Gasman2014/ThermoLogger8/Ver_3V3/Gerbers.png_Combined_Bottom.png

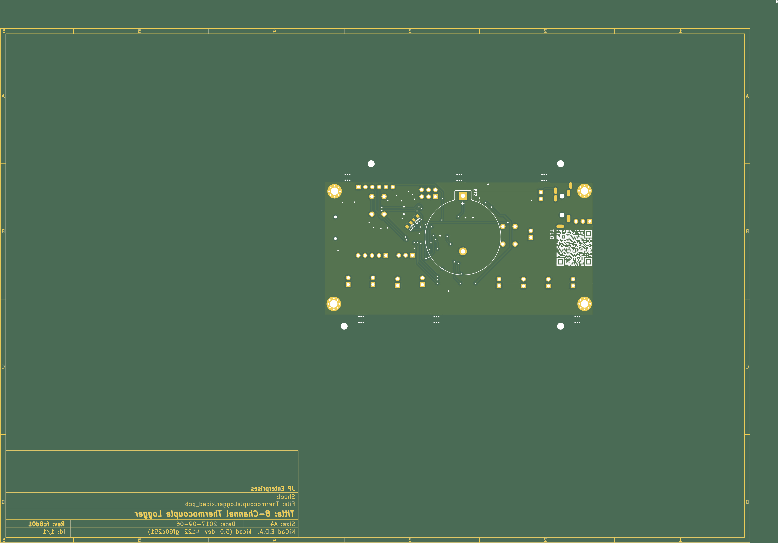
Ver_3V3/Gerbers.png_Combined_Bottom.png
