Gasman2014/ThermoLogger8/Ver_3V3/Plots/620aab/ThermocoupleLogger-B_Cu.png

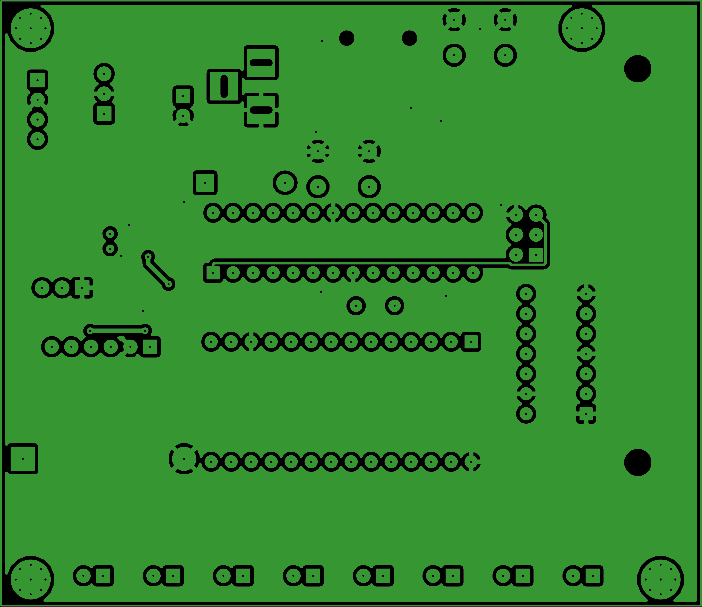
Ver_3V3/Plots/620aab/ThermocoupleLogger-B_Cu.png
