Gasman2014/ThermoLogger8/Ver_3V3/Plots/620aab/ThermocoupleLogger-Cmts_User.png

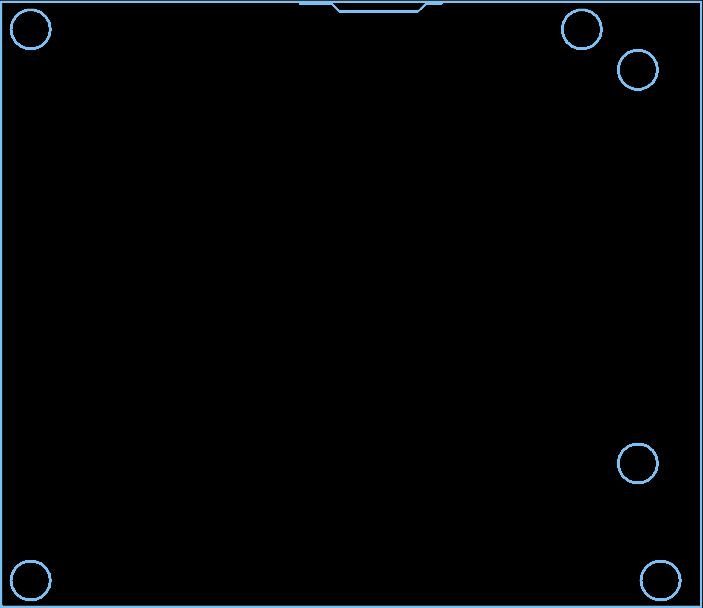
Ver_3V3/Plots/620aab/ThermocoupleLogger-Cmts_User.png
