Gasman2014/ThermoLogger8/Ver_3V3/Plots/620aab/ThermocoupleLogger-F_Fab.png

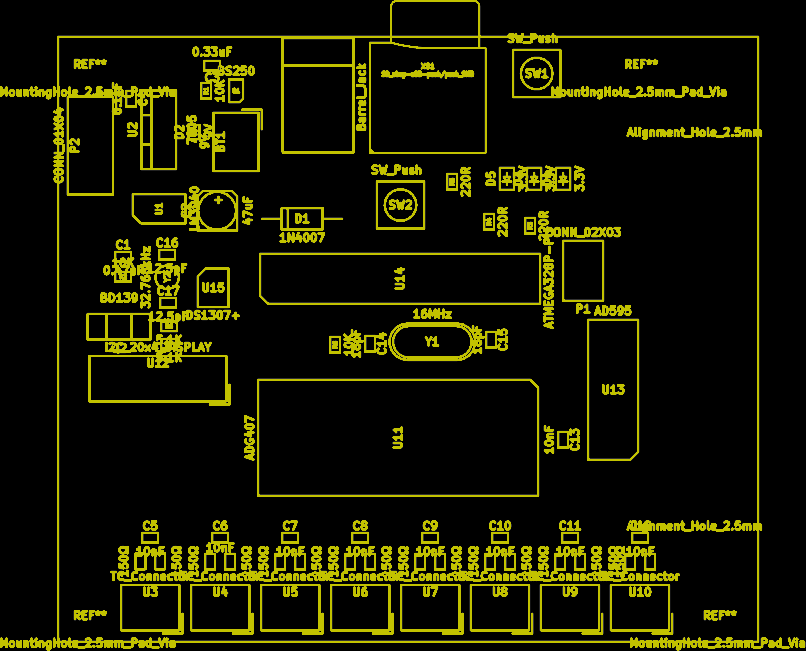
Ver_3V3/Plots/620aab/ThermocoupleLogger-F_Fab.png
