Gasman2014/ThermoLogger8/Ver_3V3/Plots/adfd4f/ThermocoupleLogger-B_CrtYd.png

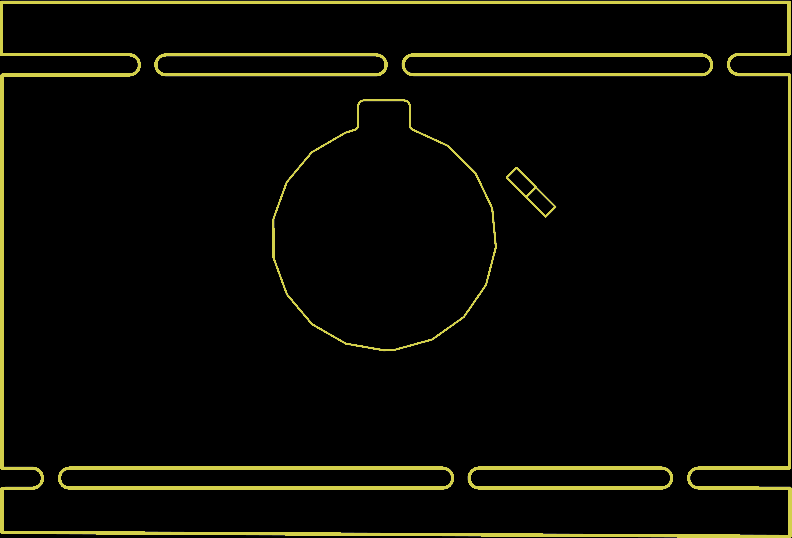
Ver_3V3/Plots/adfd4f/ThermocoupleLogger-B_CrtYd.png
