Gasman2014/ThermoLogger8/Ver_3V3/Plots/adfd4f/ThermocoupleLogger-Cmts_User.png

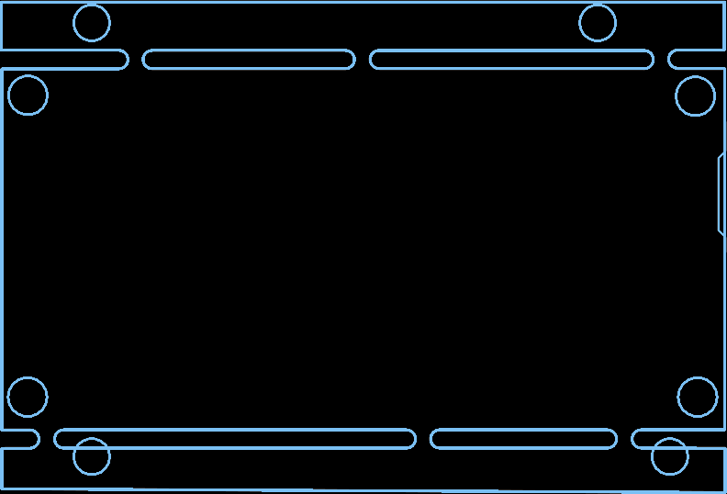
Ver_3V3/Plots/adfd4f/ThermocoupleLogger-Cmts_User.png
