Gasman2014/ThermoLogger8/Ver_3V3/Plots/adfd4f/ThermocoupleLogger-Eco2_User.png

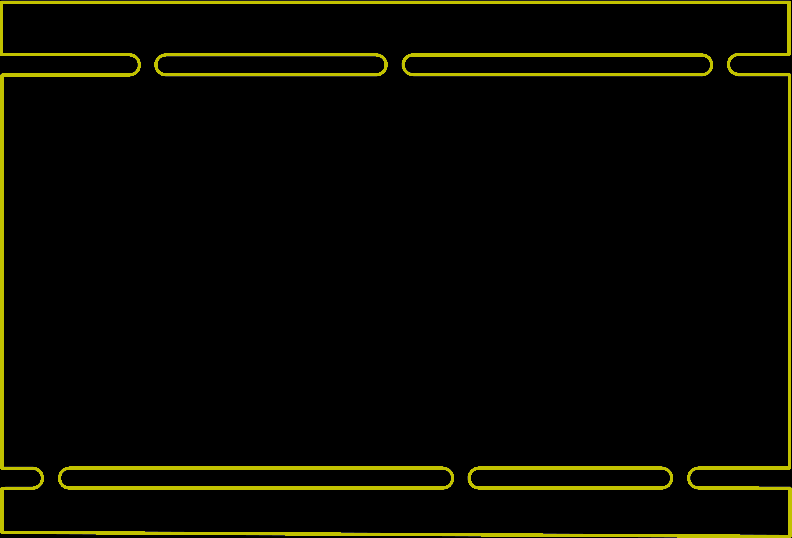
Ver_3V3/Plots/adfd4f/ThermocoupleLogger-Eco2_User.png
