Gasman2014/ThermoLogger8/Ver_3V3/Plots/adfd4f/ThermocoupleLogger-F_CrtYd.png

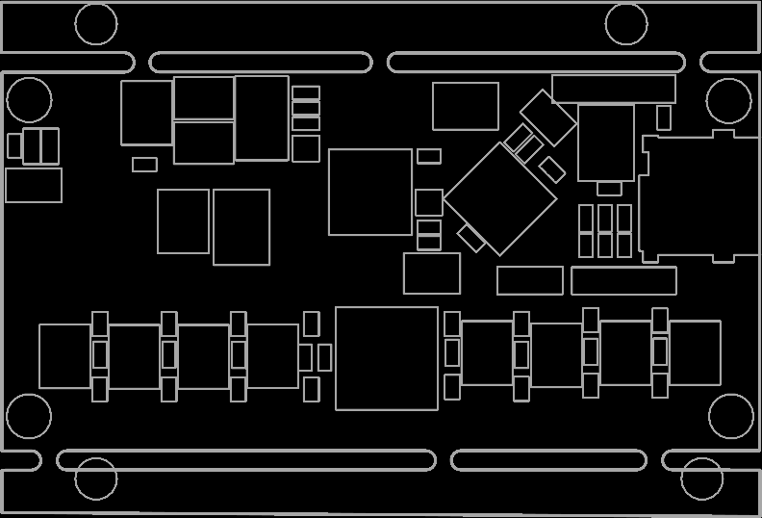
Ver_3V3/Plots/adfd4f/ThermocoupleLogger-F_CrtYd.png
