Gasman2014/ThermoLogger8/Ver_3V3/Plots/adfd4f/ThermocoupleLogger-In2_Cu.png

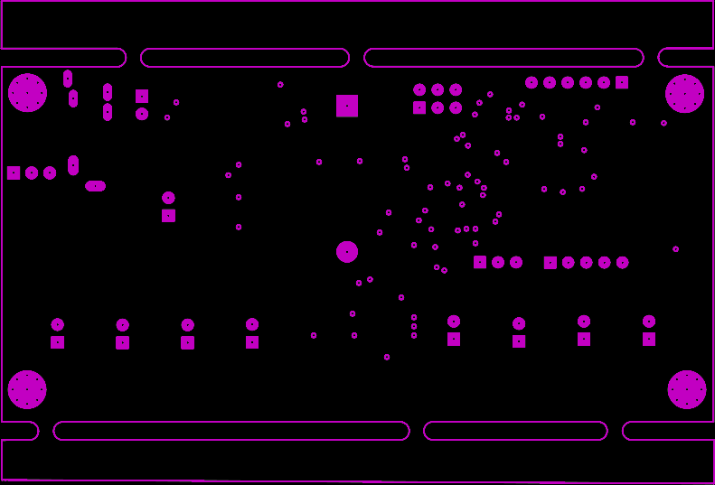
Ver_3V3/Plots/adfd4f/ThermocoupleLogger-In2_Cu.png
