Gasman2014/ThermoLogger8/Ver_3V3/Plots/web/thumbs/th_ThermocoupleLogger-B_Adhes.png

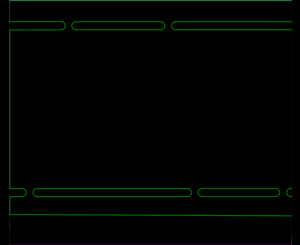
Ver_3V3/Plots/web/thumbs/th_ThermocoupleLogger-B_Adhes.png
