Gasman2014/ThermoLogger8/Ver_3V3/Plots/web/thumbs/th_ThermocoupleLogger-F_CrtYd.png

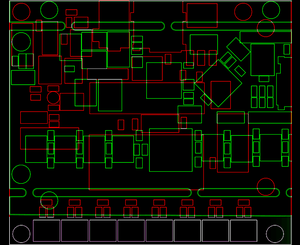
Ver_3V3/Plots/web/thumbs/th_ThermocoupleLogger-F_CrtYd.png
