Gasman2014/ThermoLogger8/Ver_5V/Plots/3c9fec/ThermocoupleLogger-B_Cu.png

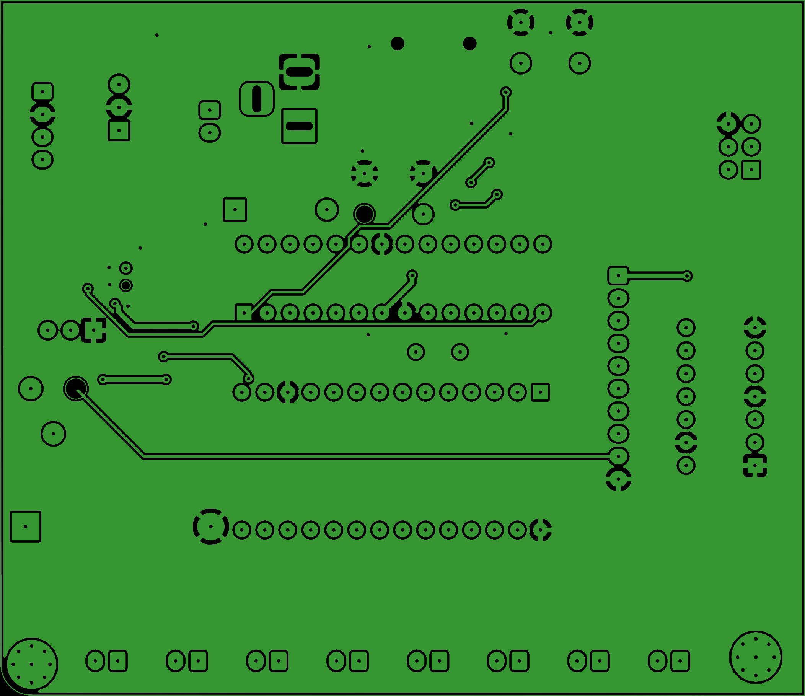
Ver_5V/Plots/3c9fec/ThermocoupleLogger-B_Cu.png
