Gasman2014/ThermoLogger8/Ver_5V/Plots/b2096b/ThermocoupleLogger-B_Mask.png

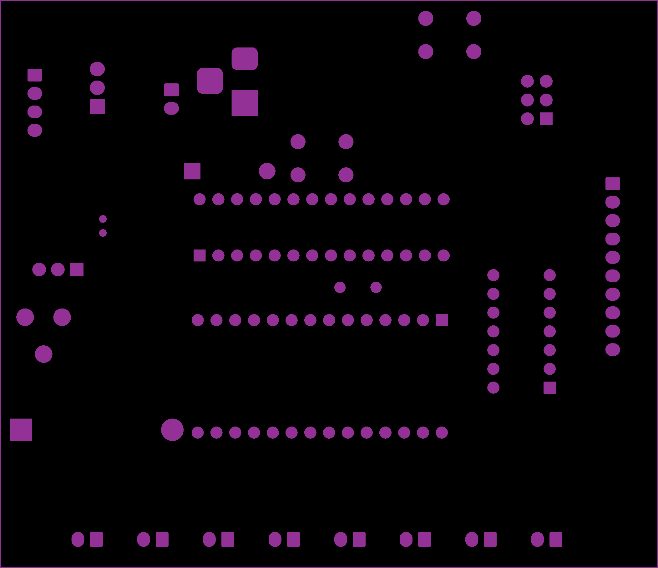
Ver_5V/Plots/b2096b/ThermocoupleLogger-B_Mask.png
