Gasman2014/ThermoLogger8/Ver_5V/Plots/b2096b/ThermocoupleLogger-F_Paste.png

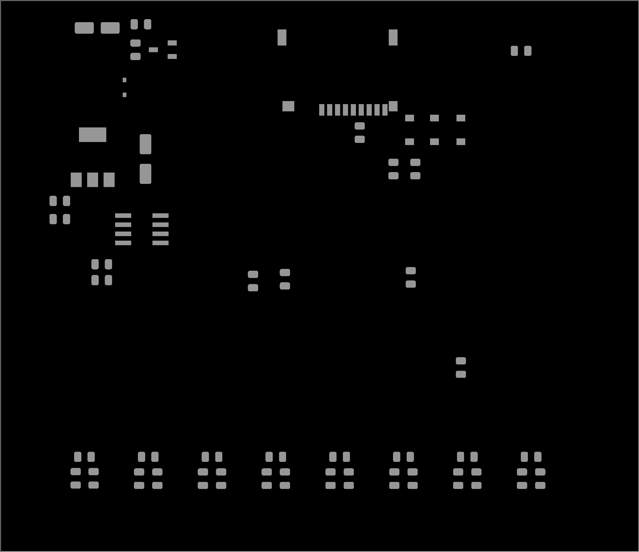
Ver_5V/Plots/b2096b/ThermocoupleLogger-F_Paste.png
