Gasman2014/ThermoLogger8/Ver_5V/Plots/b2096b/ThermocoupleLogger-In2_Cu.png

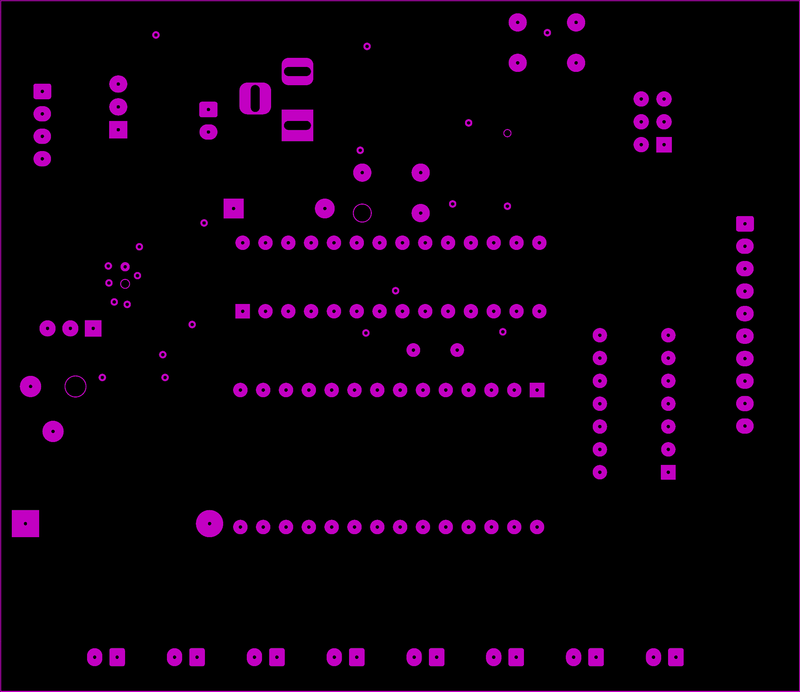
Ver_5V/Plots/b2096b/ThermocoupleLogger-In2_Cu.png
