Gasman2014/ThermoLogger8/Ver_5V/Plots/diff-3c9fec-b2096b/ThermocoupleLogger-F_CrtYd.png

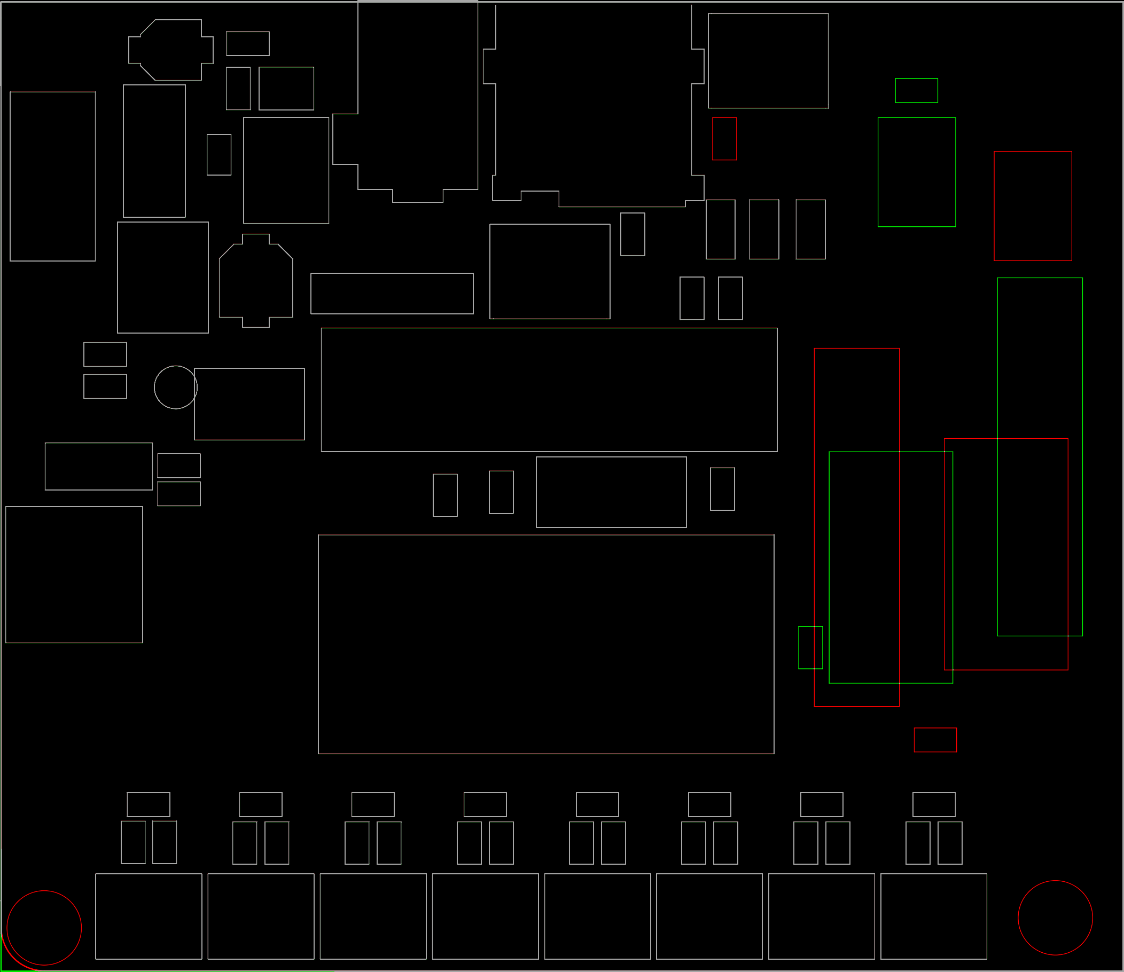
Ver_5V/Plots/diff-3c9fec-b2096b/ThermocoupleLogger-F_CrtYd.png
