Gasman2014/ThermoLogger8/Ver_5V/Plots/web/thumbs/th_ThermocoupleLogger-B_Cu.png

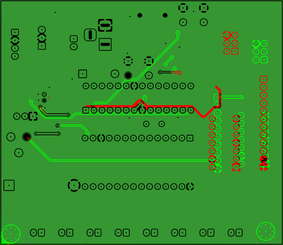
Ver_5V/Plots/web/thumbs/th_ThermocoupleLogger-B_Cu.png
