Gasman2014/ThermoLogger8/Ver_5V/Plots/web/thumbs/th_ThermocoupleLogger-F_Fab.png

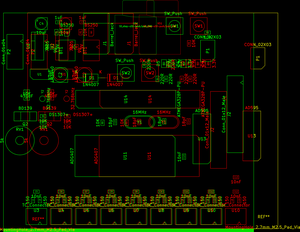
Ver_5V/Plots/web/thumbs/th_ThermocoupleLogger-F_Fab.png
