Gasman2014/ThermoLogger8/Ver_5V/Plots/diff-3c9fec-b2096b/diff.txt

5,6c5,6
<     (drawings 12)
<     (tracks 555)
---
>     (drawings 13)
>     (tracks 669)
8c8
<     (modules 73)
---
>     (modules 75)
46c46
<     (zone_clearance 0.25)
---
>     (zone_clearance 0.1)
65c65
<     (pad_size 1.1 1.3)
---
>     (pad_size 1.2 1.4)
274c274
<     (clearance 0.25)
---
>     (clearance 0.2)
287c287
<     (at 176.8 97.2 270)
---
>     (at 162.3 102.8 270)
475a476,480
>     (model ${KICUST3DMOD}/Connectors.3dshapes/BarrelJack.STEP
>       (offset (xyz -6 0 0))
>       (scale (xyz 1 1 1))
>       (rotate (xyz -90 0 -90))
>     )
1191c1196
<   (module JP_Connectors:Conn_uSDcard (layer F.Cu) (tedit 5718CF45) (tstamp 59932149)
---
>   (module JP_Connectors:Conn_uSDcard (layer F.Cu) (tedit 5C3CAC0E) (tstamp 59932149)
1340c1345
<     (at 168.275 124.841 180)
---
>     (at 177.4 123.8 180)
1559c1564
<     (at 167.8 88.4 180)
---
>     (at 177 91.1 180)
3357c3362
<     (at 158.115 123.571 270)
---
>     (at 168 130.9)
3362c3367
<     (fp_text reference C13 (at 0 -1.65 270) (layer F.SilkS)
---
>     (fp_text reference C13 (at 0 -1.65) (layer F.SilkS)
3365c3370
<     (fp_text value 10nF (at 0 1.65 270) (layer F.Fab)
---
>     (fp_text value 10nF (at 0 1.65) (layer F.Fab)
3368c3373
<     (fp_text user %R (at 0 0 270) (layer F.Fab)
---
>     (fp_text user %R (at 0 0) (layer F.Fab)
3381c3386
<     (pad 2 smd roundrect (at 0.9375 0 270) (size 0.975 1.4) (layers F.Cu F.Paste F.Mask) (roundrect_rratio 0.25)
---
>     (pad 2 smd roundrect (at 0.9375 0) (size 0.975 1.4) (layers F.Cu F.Paste F.Mask) (roundrect_rratio 0.25)
3383c3388
<     (pad 1 smd roundrect (at -0.9375 0 270) (size 0.975 1.4) (layers F.Cu F.Paste F.Mask) (roundrect_rratio 0.25)
---
>     (pad 1 smd roundrect (at -0.9375 0) (size 0.975 1.4) (layers F.Cu F.Paste F.Mask) (roundrect_rratio 0.25)
3587c3592
<     (at 166.5 79.4)
---
>     (at 151.3 83.2375 90)
3592c3597
<     (fp_text reference R9 (at 0 -1.65) (layer F.SilkS)
---
>     (fp_text reference R9 (at 0 -1.65 90) (layer F.SilkS)
3595c3600
<     (fp_text value 10K (at 0 1.65) (layer F.Fab)
---
>     (fp_text value 10K (at 0 1.65 90) (layer F.Fab)
3598c3603
<     (fp_text user %R (at 0 0) (layer F.Fab)
---
>     (fp_text user %R (at 0 0 90) (layer F.Fab)
3611c3616
<     (pad 2 smd roundrect (at 0.9375 0) (size 0.975 1.4) (layers F.Cu F.Paste F.Mask) (roundrect_rratio 0.25)
---
>     (pad 2 smd roundrect (at 0.9375 0 90) (size 0.975 1.4) (layers F.Cu F.Paste F.Mask) (roundrect_rratio 0.25)
3613c3618
<     (pad 1 smd roundrect (at -0.9375 0) (size 0.975 1.4) (layers F.Cu F.Paste F.Mask) (roundrect_rratio 0.25)
---
>     (pad 1 smd roundrect (at -0.9375 0 90) (size 0.975 1.4) (layers F.Cu F.Paste F.Mask) (roundrect_rratio 0.25)
3621a3627,3681
>   (module MountingHole:MountingHole_2.7mm_M2.5_Pad_Via (layer F.Cu) (tedit 56DDBBFF) (tstamp 5C3CC69D)
>     (at 97.4 145.8)
>     (descr "Mounting Hole 2.7mm")
>     (tags "mounting hole 2.7mm")
>     (attr virtual)
>     (fp_text reference REF** (at 0 -3.7) (layer F.SilkS)
>       (effects (font (size 1 1) (thickness 0.15)))
>     )
>     (fp_text value MountingHole_2.7mm_M2.5_Pad_Via (at 0 3.7) (layer F.Fab)
>       (effects (font (size 1 1) (thickness 0.15)))
>     )
>     (fp_circle (center 0 0) (end 2.95 0) (layer F.CrtYd) (width 0.05))
>     (fp_circle (center 0 0) (end 2.7 0) (layer Cmts.User) (width 0.15))
>     (fp_text user %R (at 0.3 0) (layer F.Fab)
>       (effects (font (size 1 1) (thickness 0.15)))
>     )
>     (pad 1 thru_hole circle (at 1.431891 -1.431891) (size 0.8 0.8) (drill 0.5) (layers *.Cu *.Mask))
>     (pad 1 thru_hole circle (at 0 -2.025) (size 0.8 0.8) (drill 0.5) (layers *.Cu *.Mask))
>     (pad 1 thru_hole circle (at -1.431891 -1.431891) (size 0.8 0.8) (drill 0.5) (layers *.Cu *.Mask))
>     (pad 1 thru_hole circle (at -2.025 0) (size 0.8 0.8) (drill 0.5) (layers *.Cu *.Mask))
>     (pad 1 thru_hole circle (at -1.431891 1.431891) (size 0.8 0.8) (drill 0.5) (layers *.Cu *.Mask))
>     (pad 1 thru_hole circle (at 0 2.025) (size 0.8 0.8) (drill 0.5) (layers *.Cu *.Mask))
>     (pad 1 thru_hole circle (at 1.431891 1.431891) (size 0.8 0.8) (drill 0.5) (layers *.Cu *.Mask))
>     (pad 1 thru_hole circle (at 2.025 0) (size 0.8 0.8) (drill 0.5) (layers *.Cu *.Mask))
>     (pad 1 thru_hole circle (at 0 0) (size 5.4 5.4) (drill 2.7) (layers *.Cu *.Mask))
>   )
> 
>   (module MountingHole:MountingHole_2.7mm_M2.5_Pad_Via (layer F.Cu) (tedit 56DDBBFF) (tstamp 5C3CC6BC)
>     (at 177.5 145)
>     (descr "Mounting Hole 2.7mm")
>     (tags "mounting hole 2.7mm")
>     (attr virtual)
>     (fp_text reference REF** (at 0 -3.7) (layer F.SilkS)
>       (effects (font (size 1 1) (thickness 0.15)))
>     )
>     (fp_text value MountingHole_2.7mm_M2.5_Pad_Via (at 0 3.7) (layer F.Fab)
>       (effects (font (size 1 1) (thickness 0.15)))
>     )
>     (fp_circle (center 0 0) (end 2.95 0) (layer F.CrtYd) (width 0.05))
>     (fp_circle (center 0 0) (end 2.7 0) (layer Cmts.User) (width 0.15))
>     (fp_text user %R (at 0.3 0) (layer F.Fab)
>       (effects (font (size 1 1) (thickness 0.15)))
>     )
>     (pad 1 thru_hole circle (at 1.431891 -1.431891) (size 0.8 0.8) (drill 0.5) (layers *.Cu *.Mask))
>     (pad 1 thru_hole circle (at 0 -2.025) (size 0.8 0.8) (drill 0.5) (layers *.Cu *.Mask))
>     (pad 1 thru_hole circle (at -1.431891 -1.431891) (size 0.8 0.8) (drill 0.5) (layers *.Cu *.Mask))
>     (pad 1 thru_hole circle (at -2.025 0) (size 0.8 0.8) (drill 0.5) (layers *.Cu *.Mask))
>     (pad 1 thru_hole circle (at -1.431891 1.431891) (size 0.8 0.8) (drill 0.5) (layers *.Cu *.Mask))
>     (pad 1 thru_hole circle (at 0 2.025) (size 0.8 0.8) (drill 0.5) (layers *.Cu *.Mask))
>     (pad 1 thru_hole circle (at 1.431891 1.431891) (size 0.8 0.8) (drill 0.5) (layers *.Cu *.Mask))
>     (pad 1 thru_hole circle (at 2.025 0) (size 0.8 0.8) (drill 0.5) (layers *.Cu *.Mask))
>     (pad 1 thru_hole circle (at 0 0) (size 5.4 5.4) (drill 2.7) (layers *.Cu *.Mask))
>   )
> 
>   (gr_arc (start 97.4 145.8) (end 94 145.8) (angle -90) (layer Edge.Cuts) (width 0.1))
3625c3685
<   (gr_text "©2017, JP Enterprises" (at 95.758 102.616 270) (layer F.SilkS)
---
>   (gr_text "©2019, JP Enterprises" (at 95.758 102.616 270) (layer F.SilkS)
3640,3641c3700,3701
<   (gr_line (start 93.98 149.225) (end 182.88 149.225) (layer Edge.Cuts) (width 0.1))
<   (gr_line (start 93.98 72.39) (end 93.98 149.225) (layer Edge.Cuts) (width 0.1))
---
>   (gr_line (start 97.4 149.2) (end 182.88 149.225) (layer Edge.Cuts) (width 0.1))
>   (gr_line (start 93.98 72.39) (end 94 145.8) (layer Edge.Cuts) (width 0.1))
3667,3668d3726
<   (segment (start 158.115 122.571) (end 160.385 122.571) (width 0.5) (layer F.Cu) (net 1) (status 30))
<   (segment (start 160.385 122.571) (end 160.655 122.301) (width 0.5) (layer F.Cu) (net 1) (status 30))
3706d3763
<   (via (at 109.1946 102.9716) (size 0.8) (drill 0.4) (layers F.Cu B.Cu) (net 1))
3726a3784,3788
>   (segment (start 167.0625 129.9375) (end 167.0625 130.9) (width 0.5) (layer F.Cu) (net 1) (status 20))
>   (segment (start 162.425 125.3) (end 167.0625 129.9375) (width 0.5) (layer F.Cu) (net 1) (status 10))
>   (segment (start 162.3 125.3) (end 162.425 125.3) (width 0.5) (layer F.Cu) (net 1) (status 30))
>   (segment (start 112.6005 78.135) (end 112.776 78.3105) (width 0.5) (layer F.Cu) (net 1))
>   (segment (start 112.6005 75.692) (end 112.6005 78.135) (width 0.5) (layer F.Cu) (net 1))
3731d3792
<   (segment (start 115.279426 108.407535) (end 108.449333 108.407535) (width 0.5) (layer B.Cu) (net 2))
3734,3735d3794
<   (segment (start 106.611743 106.569945) (end 106.611743 105.899326) (width 0.5) (layer B.Cu) (net 2))
<   (segment (start 108.449333 108.407535) (end 106.611743 106.569945) (width 0.5) (layer B.Cu) (net 2))
3742a3802,3805
>   (segment (start 115.279426 108.407535) (end 108.611433 108.407535) (width 0.5) (layer B.Cu) (net 2))
>   (segment (start 108.611433 108.407535) (end 107.011742 106.807844) (width 0.5) (layer B.Cu) (net 2))
>   (segment (start 107.011742 106.807844) (end 107.011742 106.299325) (width 0.5) (layer B.Cu) (net 2))
>   (segment (start 107.011742 106.299325) (end 106.611743 105.899326) (width 0.5) (layer B.Cu) (net 2))
3767,3773d3829
<   (segment (start 141.224 100.44537) (end 140.716 100.95337) (width 0.5) (layer F.Cu) (net 3))
<   (segment (start 141.224 99.314) (end 141.224 100.44537) (width 0.5) (layer F.Cu) (net 3) (status 10))
<   (segment (start 140.716 100.95337) (end 140.716 101.854) (width 0.5) (layer F.Cu) (net 3))
<   (via (at 137.922 104.648) (size 0.8) (drill 0.4) (layers F.Cu B.Cu) (net 3))
<   (segment (start 140.716 101.854) (end 137.922 104.648) (width 0.5) (layer F.Cu) (net 3))
<   (segment (start 137.922 104.648) (end 137.922 105.156) (width 0.5) (layer B.Cu) (net 3))
<   (segment (start 137.922 105.156) (end 136.144 106.934) (width 0.5) (layer B.Cu) (net 3) (status 20))
3785,3788c3841,3865
<   (segment (start 102.23754 101.27004) (end 101.2975 100.33) (width 0.5) (layer F.Cu) (net 3) (status 20))
<   (segment (start 102.23754 104.335556) (end 102.23754 101.27004) (width 0.5) (layer F.Cu) (net 3))
<   (segment (start 102.318556 104.335556) (end 107.1395 109.1565) (width 0.5) (layer F.Cu) (net 3) (status 20))
<   (segment (start 102.23754 104.335556) (end 102.318556 104.335556) (width 0.5) (layer F.Cu) (net 3))
---
>   (segment (start 139.481795 103.596205) (end 139.481795 102.774979) (width 0.5) (layer B.Cu) (net 3))
>   (via (at 139.481795 102.774979) (size 0.8) (drill 0.4) (layers F.Cu B.Cu) (net 3))
>   (segment (start 141.224 101.032774) (end 139.481795 102.774979) (width 0.5) (layer F.Cu) (net 3))
>   (segment (start 141.224 99.314) (end 141.224 101.032774) (width 0.5) (layer F.Cu) (net 3) (status 10))
>   (segment (start 136.144 106.934) (end 139.481795 103.596205) (width 0.5) (layer B.Cu) (net 3) (status 10))
>   (segment (start 153.67 119.259338) (end 153.67 115.697) (width 0.5) (layer F.Cu) (net 3) (status 20))
>   (segment (start 166.510672 132.10001) (end 153.67 119.259338) (width 0.5) (layer F.Cu) (net 3))
>   (segment (start 169.489328 132.10001) (end 166.510672 132.10001) (width 0.5) (layer F.Cu) (net 3))
>   (segment (start 171.080001 130.509337) (end 169.489328 132.10001) (width 0.5) (layer F.Cu) (net 3))
>   (segment (start 171.080001 118.095999) (end 171.080001 130.509337) (width 0.5) (layer F.Cu) (net 3))
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
<   (segment (start 140.927 88.68) (end 142.92701 90.68001) (width 0.25) (layer F.Cu) (net 26))
---
>   (segment (start 153.432 92.924) (end 154.282 92.074) (width 0.25) (layer F.Cu) (net 26) (status 20))
>   (segment (start 147.408413 92.924) (end 153.432 92.924) (width 0.25) (layer F.Cu) (net 26))
>   (segment (start 147.3 92.815587) (end 147.408413 92.924) (width 0.25) (layer F.Cu) (net 26))
>   (segment (start 147.3 93.5305) (end 147.3 92.815587) (width 0.25) (layer F.Cu) (net 26))
>   (segment (start 148.717 94.9475) (end 147.3 93.5305) (width 0.25) (layer F.Cu) (net 26) (status 10))
>   (segment (start 142.92701 90.68001) (end 145.253012 90.68001) (width 0.25) (layer F.Cu) (net 26))
3985a4062,4064
>   (segment (start 140.927 88.68) (end 142.92701 90.68001) (width 0.25) (layer F.Cu) (net 26))
>   (segment (start 145.253012 90.68001) (end 147.3 92.726998) (width 0.25) (layer F.Cu) (net 26))
>   (segment (start 147.3 92.726998) (end 147.3 92.815587) (width 0.25) (layer F.Cu) (net 26))
3994,3998c4073,4077
<   (segment (start 150.114 94.996) (end 150.368 95.25) (width 0.25) (layer B.Cu) (net 27))
<   (via (at 150.368 95.25) (size 0.8) (drill 0.4) (layers F.Cu B.Cu) (net 27))
<   (segment (start 144.272 94.996) (end 150.114 94.996) (width 0.25) (layer B.Cu) (net 27))
<   (segment (start 151.4625 95.25) (end 151.765 94.9475) (width 0.25) (layer F.Cu) (net 27) (status 30))
<   (segment (start 150.368 95.25) (end 151.4625 95.25) (width 0.25) (layer F.Cu) (net 27) (status 20))
---
>   (segment (start 151.765 94.9475) (end 150.64353 93.82603) (width 0.25) (layer F.Cu) (net 27) (status 10))
>   (segment (start 144.272 94.996) (end 147.694734 94.996) (width 0.25) (layer B.Cu) (net 27))
>   (segment (start 147.694734 94.996) (end 148.864704 93.82603) (width 0.25) (layer B.Cu) (net 27))
>   (segment (start 150.64353 93.82603) (end 148.864704 93.82603) (width 0.25) (layer F.Cu) (net 27))
>   (via (at 148.864704 93.82603) (size 0.8) (drill 0.4) (layers F.Cu B.Cu) (net 27))
4052,4057d4130
<   (segment (start 158.011 79.303) (end 158.011 80.717213) (width 0.25) (layer F.Cu) (net 45) (status 10))
<   (segment (start 158.011 80.717213) (end 160.147 82.853213) (width 0.25) (layer F.Cu) (net 45))
<   (segment (start 160.147 82.853213) (end 160.147 84.709) (width 0.25) (layer F.Cu) (net 45))
<   (segment (start 155.502787 84.709) (end 160.147 84.709) (width 0.25) (layer F.Cu) (net 45))
<   (segment (start 151.511 79.303) (end 151.511 80.717213) (width 0.25) (layer F.Cu) (net 45) (status 10))
<   (segment (start 151.511 80.717213) (end 155.502787 84.709) (width 0.25) (layer F.Cu) (net 45))
4058a4132,4150
>   (segment (start 151.511 79.303) (end 158.011 79.303) (width 0.25) (layer F.Cu) (net 45) (status 30))
>   (segment (start 170.283 79.303) (end 177 86.02) (width 0.25) (layer F.Cu) (net 45) (status 20))
>   (segment (start 158.011 79.303) (end 170.283 79.303) (width 0.25) (layer F.Cu) (net 45) (status 10))
>   (segment (start 151.511 82.089) (end 151.3 82.3) (width 0.25) (layer F.Cu) (net 45) (status 30))
>   (segment (start 151.511 79.303) (end 151.511 82.089) (width 0.25) (layer F.Cu) (net 45) (status 30))
>   (via (at 149.85 82.52) (size 0.8) (drill 0.4) (layers F.Cu B.Cu) (net 45))
>   (segment (start 151.08 82.52) (end 151.3 82.3) (width 0.25) (layer F.Cu) (net 45) (status 30))
>   (segment (start 149.85 82.52) (end 151.08 82.52) (width 0.25) (layer F.Cu) (net 45) (status 20))
>   (segment (start 120.904 106.934) (end 121.200476 107.230476) (width 0.25) (layer F.Cu) (net 45) (status 30))
>   (segment (start 123.940464 104.644003) (end 121.600475 106.983992) (width 0.25) (layer B.Cu) (net 45) (status 20))
>   (segment (start 127.398999 104.644003) (end 123.940464 104.644003) (width 0.25) (layer B.Cu) (net 45))
>   (segment (start 121.200476 107.230476) (end 121.200476 107.383991) (width 0.25) (layer F.Cu) (net 45) (status 30))
>   (segment (start 121.600475 106.983992) (end 121.200476 107.383991) (width 0.25) (layer B.Cu) (net 45) (status 30))
>   (segment (start 149.85 84.413002) (end 136.926001 97.337001) (width 0.25) (layer B.Cu) (net 45))
>   (segment (start 132.478999 98.571001) (end 132.478999 99.564003) (width 0.25) (layer B.Cu) (net 45))
>   (segment (start 132.478999 99.564003) (end 127.398999 104.644003) (width 0.25) (layer B.Cu) (net 45))
>   (segment (start 136.926001 97.337001) (end 133.712999 97.337001) (width 0.25) (layer B.Cu) (net 45))
>   (segment (start 133.712999 97.337001) (end 132.478999 98.571001) (width 0.25) (layer B.Cu) (net 45))
>   (segment (start 149.85 82.52) (end 149.85 84.413002) (width 0.25) (layer B.Cu) (net 45))
4060a4153,4166
>   (segment (start 152.509001 99.854001) (end 151.924001 100.439001) (width 0.25) (layer F.Cu) (net 46))
>   (segment (start 151.924001 100.439001) (end 149.969001 100.439001) (width 0.25) (layer F.Cu) (net 46))
>   (segment (start 174.46 88.56) (end 175.635001 89.735001) (width 0.25) (layer F.Cu) (net 46))
>   (segment (start 170.408402 104.085013) (end 169.141598 104.085013) (width 0.25) (layer F.Cu) (net 46))
>   (segment (start 177.920003 89.735001) (end 178.175001 89.989999) (width 0.25) (layer F.Cu) (net 46))
>   (segment (start 178.175001 89.989999) (end 178.175001 96.318414) (width 0.25) (layer F.Cu) (net 46))
>   (segment (start 169.141598 104.085013) (end 163.245584 98.188999) (width 0.25) (layer F.Cu) (net 46))
>   (segment (start 175.635001 89.735001) (end 177.920003 89.735001) (width 0.25) (layer F.Cu) (net 46))
>   (segment (start 178.175001 96.318414) (end 170.408402 104.085013) (width 0.25) (layer F.Cu) (net 46))
>   (segment (start 153.383999 98.188999) (end 152.509001 99.063997) (width 0.25) (layer F.Cu) (net 46))
>   (segment (start 152.509001 99.063997) (end 152.509001 99.854001) (width 0.25) (layer F.Cu) (net 46))
>   (segment (start 163.245584 98.188999) (end 153.383999 98.188999) (width 0.25) (layer F.Cu) (net 46))
>   (segment (start 149.969001 100.439001) (end 149.643999 100.113999) (width 0.25) (layer F.Cu) (net 46))
>   (segment (start 149.643999 100.113999) (end 148.844 99.314) (width 0.25) (layer F.Cu) (net 46))
4064a4171,4197
>   (segment (start 159.015001 89.599001) (end 148.427597 89.599001) (width 0.25) (layer F.Cu) (net 47))
>   (segment (start 148 90.026598) (end 148 90.3) (width 0.25) (layer F.Cu) (net 47))
>   (segment (start 161.229003 87.384999) (end 159.015001 89.599001) (width 0.25) (layer F.Cu) (net 47))
>   (segment (start 148.427597 89.599001) (end 148 90.026598) (width 0.25) (layer F.Cu) (net 47))
>   (segment (start 175.824999 87.384999) (end 161.229003 87.384999) (width 0.25) (layer F.Cu) (net 47))
>   (via (at 148 90.3) (size 0.8) (drill 0.4) (layers F.Cu B.Cu) (net 47))
>   (segment (start 177 88.56) (end 175.824999 87.384999) (width 0.25) (layer F.Cu) (net 47) (status 10))
>   (via (at 146 92.5) (size 0.8) (drill 0.4) (layers F.Cu B.Cu) (net 47))
>   (segment (start 146 92.3) (end 146 92.5) (width 0.25) (layer B.Cu) (net 47))
>   (segment (start 148 90.3) (end 146 92.3) (width 0.25) (layer B.Cu) (net 47))
>   (segment (start 144.7755 92.5) (end 144.018 91.7425) (width 0.25) (layer F.Cu) (net 47) (status 20))
>   (segment (start 146 92.5) (end 144.7755 92.5) (width 0.25) (layer F.Cu) (net 47))
>   (segment (start 146.304 97.73115) (end 148.27514 95.76001) (width 0.25) (layer F.Cu) (net 48))
>   (segment (start 146.304 99.314) (end 146.304 97.73115) (width 0.25) (layer F.Cu) (net 48) (status 10))
>   (segment (start 158.975001 91.298999) (end 161.876002 94.2) (width 0.25) (layer F.Cu) (net 48))
>   (segment (start 145.327 88.68) (end 147.945999 91.298999) (width 0.25) (layer F.Cu) (net 48))
>   (segment (start 145.327 87.63) (end 145.327 88.68) (width 0.25) (layer F.Cu) (net 48) (status 10))
>   (segment (start 147.945999 91.298999) (end 158.975001 91.298999) (width 0.25) (layer F.Cu) (net 48))
>   (segment (start 161.876002 94.336012) (end 163.3 95.76001) (width 0.25) (layer F.Cu) (net 48))
>   (segment (start 161.876002 94.2) (end 161.876002 94.336012) (width 0.25) (layer F.Cu) (net 48))
>   (segment (start 148.27514 95.76001) (end 163.3 95.76001) (width 0.25) (layer F.Cu) (net 48))
>   (segment (start 169.307998 103.615002) (end 170.242002 103.615002) (width 0.25) (layer F.Cu) (net 48))
>   (segment (start 163.3 95.76001) (end 163.3 97.607004) (width 0.25) (layer F.Cu) (net 48))
>   (segment (start 163.3 97.607004) (end 169.307998 103.615002) (width 0.25) (layer F.Cu) (net 48))
>   (segment (start 177 96.857004) (end 177 92.2) (width 0.25) (layer F.Cu) (net 48))
>   (segment (start 177 92.2) (end 177 91.1) (width 0.25) (layer F.Cu) (net 48))
>   (segment (start 170.242002 103.615002) (end 177 96.857004) (width 0.25) (layer F.Cu) (net 48))
4122,4135c4255,4264
<   (segment (start 142.638999 95.973997) (end 142.638999 99.854001) (width 0.25) (layer F.Cu) (net 52))
<   (segment (start 142.638999 99.854001) (end 148.093986 105.308988) (width 0.25) (layer F.Cu) (net 52))
<   (segment (start 148.093986 105.308988) (end 152.298988 105.308988) (width 0.25) (layer F.Cu) (net 52))
<   (segment (start 103.1725 102.87) (end 105.456888 100.585612) (width 0.25) (layer F.Cu) (net 52) (status 10))
<   (segment (start 115.680613 97.934999) (end 131.528601 97.934999) (width 0.25) (layer F.Cu) (net 52))
<   (segment (start 131.528601 97.934999) (end 132.890999 96.572601) (width 0.25) (layer F.Cu) (net 52))
<   (segment (start 153.124001 106.134001) (end 153.924 106.934) (width 0.25) (layer F.Cu) (net 52) (status 30))
<   (segment (start 141.352001 94.686999) (end 142.638999 95.973997) (width 0.25) (layer F.Cu) (net 52))
<   (segment (start 133.579999 94.686999) (end 141.352001 94.686999) (width 0.25) (layer F.Cu) (net 52))
<   (segment (start 105.456888 100.585612) (end 113.03 100.585612) (width 0.25) (layer F.Cu) (net 52))
<   (segment (start 113.03 100.585612) (end 115.680613 97.934999) (width 0.25) (layer F.Cu) (net 52))
<   (segment (start 132.890999 96.572601) (end 132.890999 95.375999) (width 0.25) (layer F.Cu) (net 52))
<   (segment (start 132.890999 95.375999) (end 133.579999 94.686999) (width 0.25) (layer F.Cu) (net 52))
<   (segment (start 152.298988 105.308988) (end 153.124001 106.134001) (width 0.25) (layer F.Cu) (net 52) (status 20))
---
>   (segment (start 108.107897 109.3) (end 103.61999 104.812093) (width 0.25) (layer B.Cu) (net 52))
>   (via (at 103.61999 104.246408) (size 0.8) (drill 0.4) (layers F.Cu B.Cu) (net 52))
>   (segment (start 103.61999 104.812093) (end 103.61999 104.246408) (width 0.25) (layer B.Cu) (net 52))
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
>         (xy 140.538394 112.207424) (xy 140.855424 111.890394) (xy 141.027 111.476174) (xy 141.027 111.027826) (xy 143.653 111.027826)
>         (xy 143.653 111.476174) (xy 143.824576 111.890394) (xy 144.141606 112.207424) (xy 144.555826 112.379) (xy 145.004174 112.379)
>         (xy 145.418394 112.207424) (xy 145.735424 111.890394) (xy 145.907 111.476174) (xy 145.907 111.027826) (xy 145.735424 110.613606)
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
